ElectronicCats/CatWAN_USB_Stick/Fw/LoRa_PHY/LoRaReceiver/LoRaReceiver.ino

/**
 * Example LoRaReceiver
 * Authors: Electronic Cats
 * 
 * This code is beerware; if you see me (or any other collaborator 
 * member) at the local, and you've found our code helpful, 
 * please buy us a round!
 * Distributed as-is; no warranty is given.
 */
#include <SPI.h>
#include <LoRa.h>

#define SS 17
#define RFM_RST 21
#define RFM_DIO0 10
#define RFM_DIO5 15

void setup() {
  Serial.begin(9600);
  while (!Serial);

  Serial.println("LoRa Receiver");
  LoRa.setPins(SS, RFM_RST, RFM_DIO0);
  if (!LoRa.begin(915E6)) {
    Serial.println("Starting LoRa failed!");
    while (1);
  }
}

void loop() {
  // try to parse packet
  int packetSize = LoRa.parsePacket();
  if (packetSize) {
    // received a packet
    Serial.print("Received packet '");

    // read packet
    while (LoRa.available()) {
      Serial.print((char)LoRa.read());
    }

    // print RSSI of packet
    Serial.print("' with RSSI ");
    Serial.println(LoRa.packetRssi());
  }
}
